Kithdara/Simple-Voice-Recorder/Prototype on breadboard.jpeg

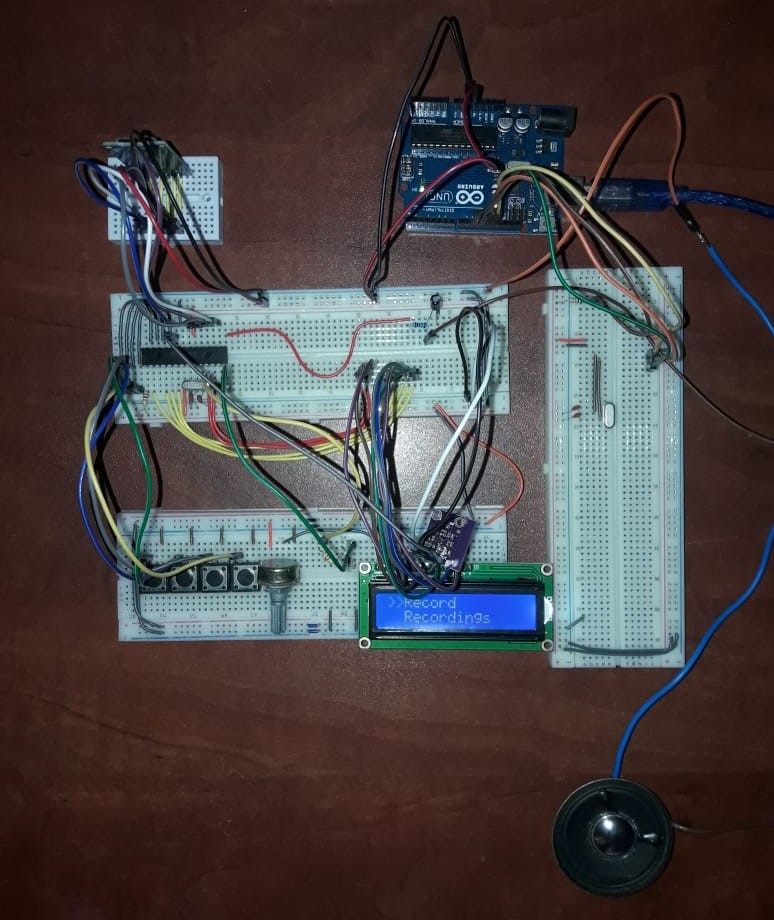
Prototype on breadboard.jpeg
