Kithdara/Simple-Voice-Recorder/simulations of spectrum changes/Downsampling/Photos/DownSampling Spectrum.png

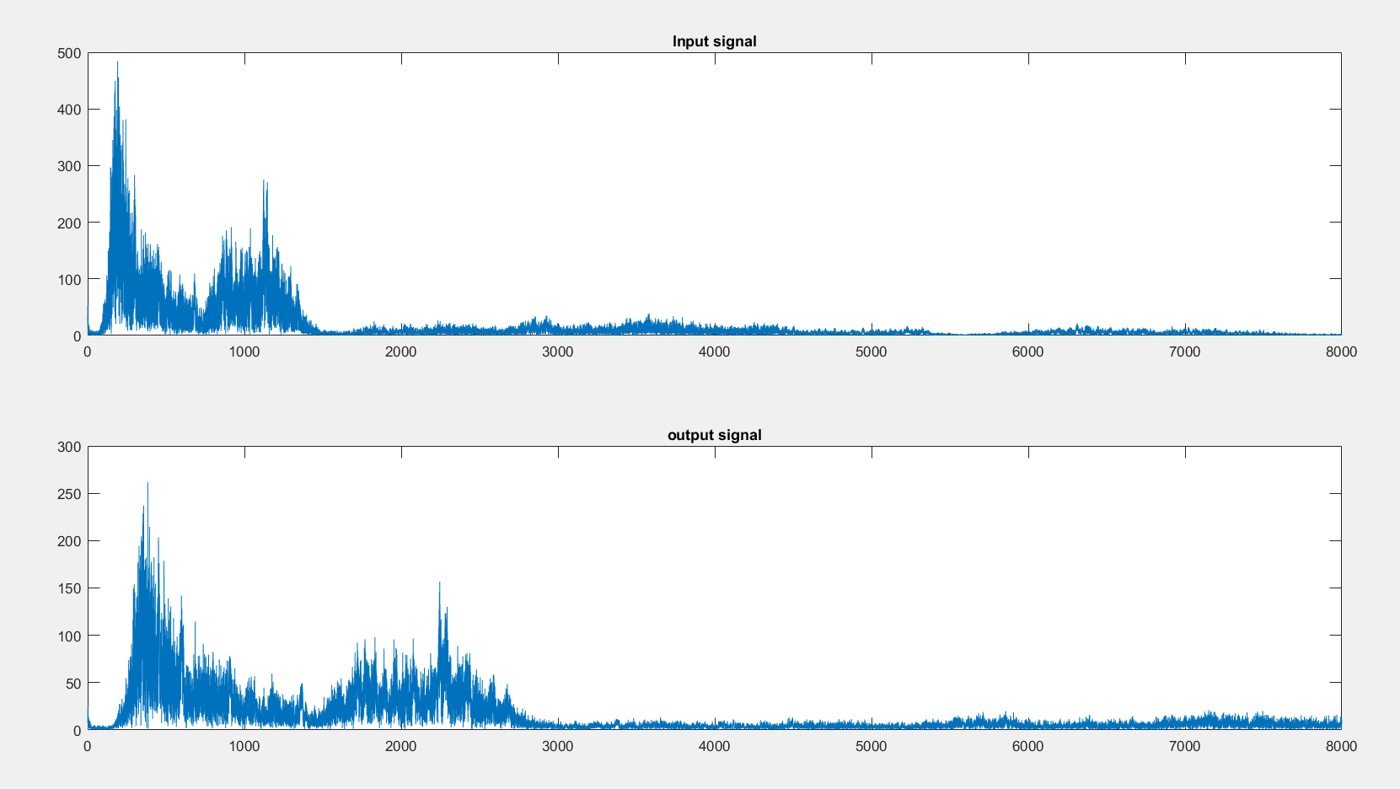
simulations of spectrum changes/Downsampling/Photos/DownSampling Spectrum.png
