Kithdara/Simple-Voice-Recorder/Final Enclousre Design/battery-9v-pile-9v-1.snapshot.1/Connecteur femelle Batterie 9V.SLDPRT

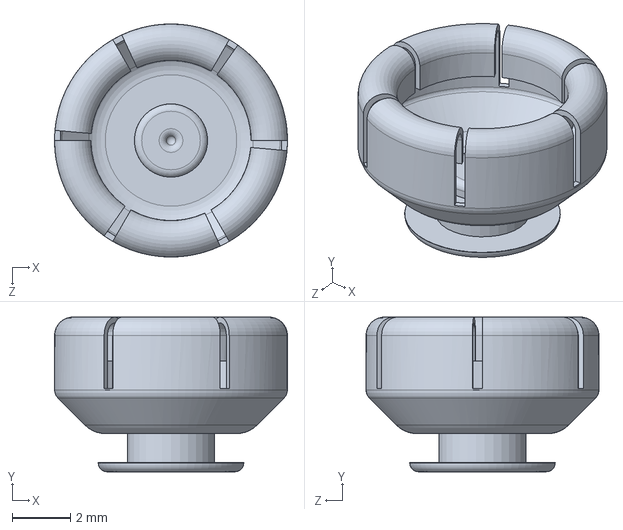
[picture p45: CAD file, 2021-09-02]
Final Enclousre Design/battery-9v-pile-9v-1.snapshot.1/Connecteur femelle Batterie 9V.SLDPRT
8.00 x 5.31 x 8.00 mm
