Kithdara/Simple-Voice-Recorder/Final Enclousre Design/Name plate.SLDPRT

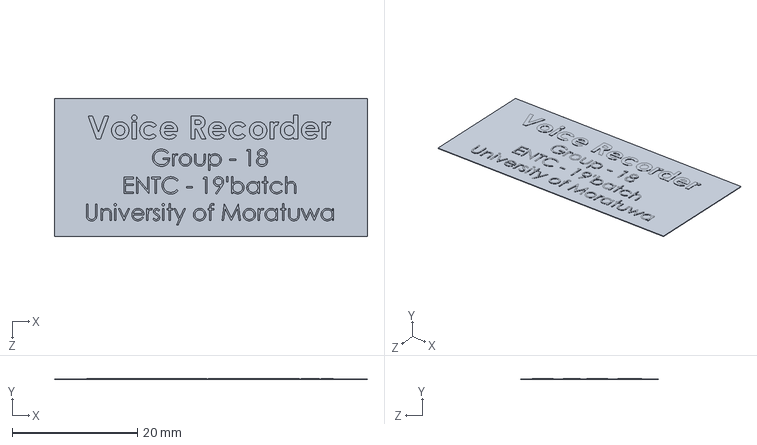
[picture p46: CAD file, 2021-09-02]
Final Enclousre Design/Name plate.SLDPRT
50.0 x 0.15 x 22.0 mm
