Kithdara/Simple-Voice-Recorder/Final Enclousre Design/battery-9v-pile-9v-1.snapshot.1/Corps Batterie.SLDPRT

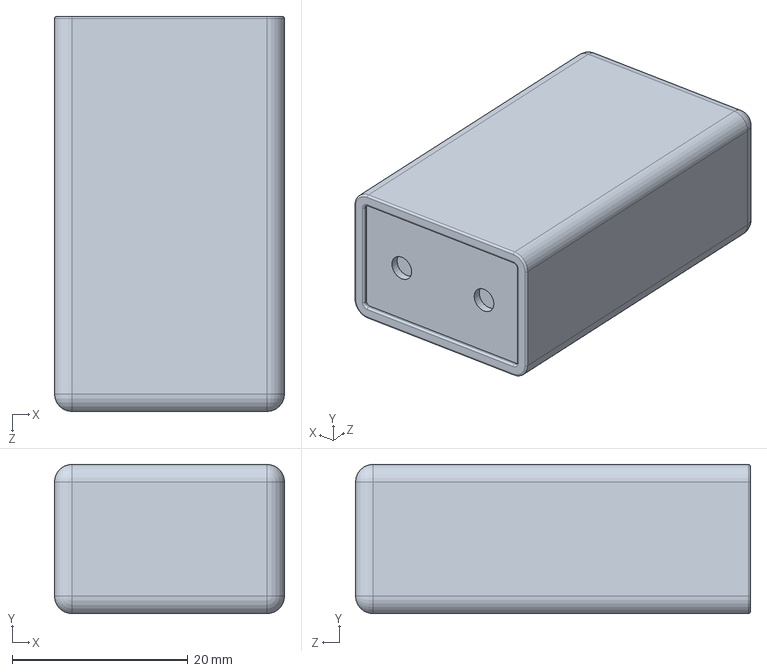
[picture p47: CAD file, 2021-09-02]
Final Enclousre Design/battery-9v-pile-9v-1.snapshot.1/Corps Batterie.SLDPRT
26.2 x 17.0 x 45.0 mm
