Kithdara/Simple-Voice-Recorder/Final Enclousre Design/button.SLDPRT

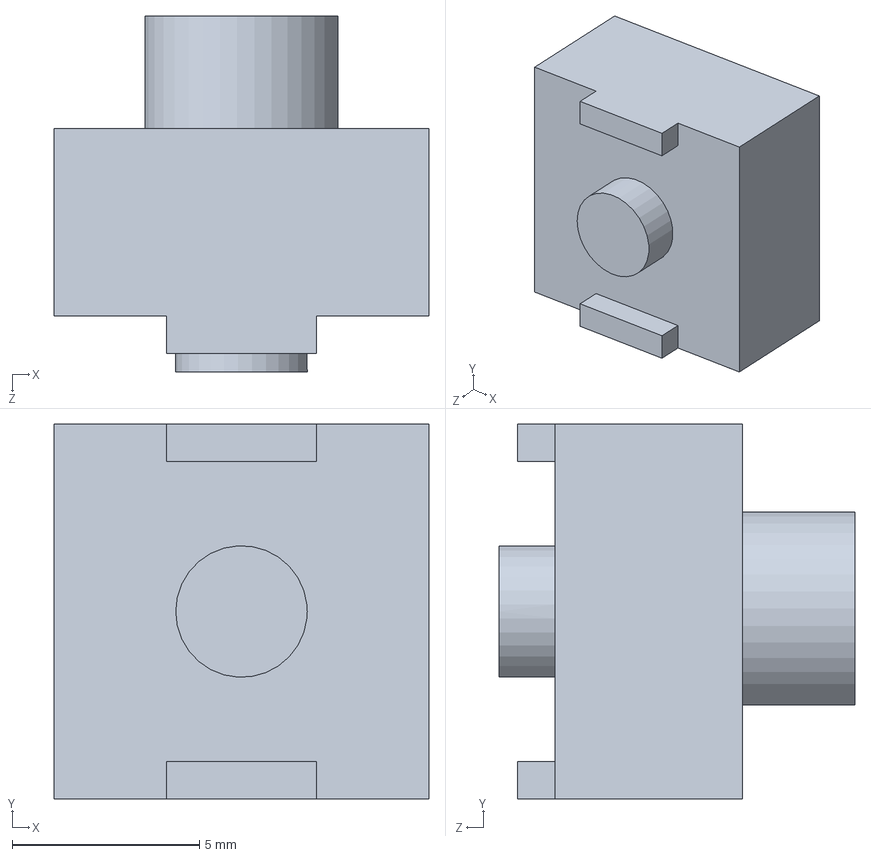
[picture p48: CAD file, 2021-09-02]
Final Enclousre Design/button.SLDPRT
10.0 x 10.0 x 9.50 mm
