Kithdara/Simple-Voice-Recorder/Final Enclousre Design/battery-9v-pile-9v-1.snapshot.1/Connecteur male Batterie 9V.SLDPRT

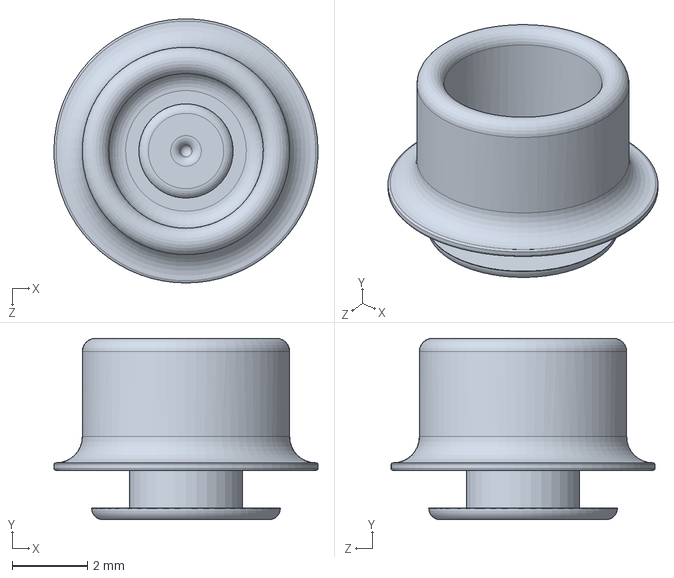
[picture p49: CAD file, 2021-09-02]
Final Enclousre Design/battery-9v-pile-9v-1.snapshot.1/Connecteur male Batterie 9V.SLDPRT
7.00 x 4.81 x 7.00 mm
