Kithdara/Simple-Voice-Recorder/Final Enclousre Design/recorder top.SLDPRT

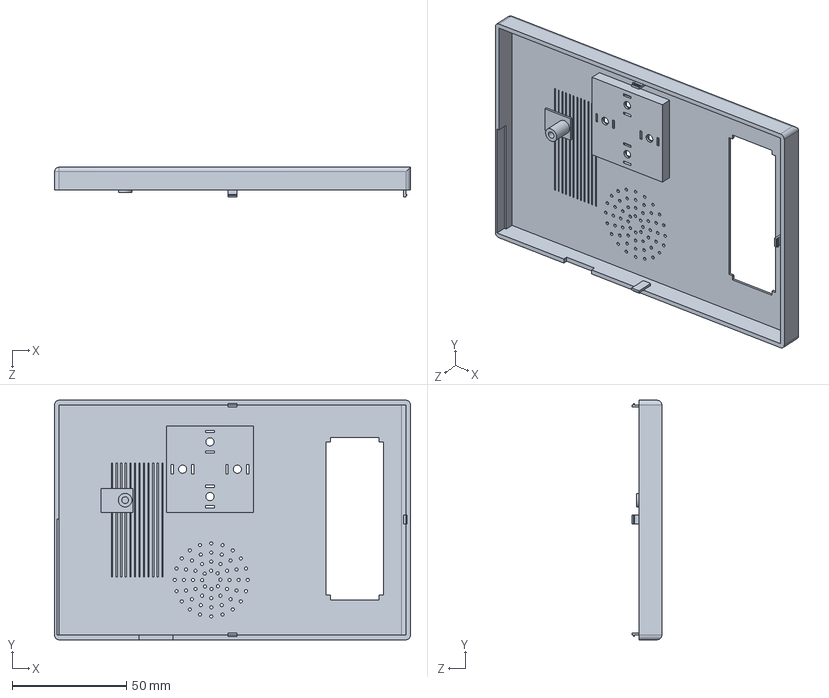
[picture p50: CAD file, 2021-09-02]
Final Enclousre Design/recorder top.SLDPRT
156.0 x 105.0 x 13.0 mm
