Kithdara/Simple-Voice-Recorder/Final Enclousre Design/battery cover.SLDPRT

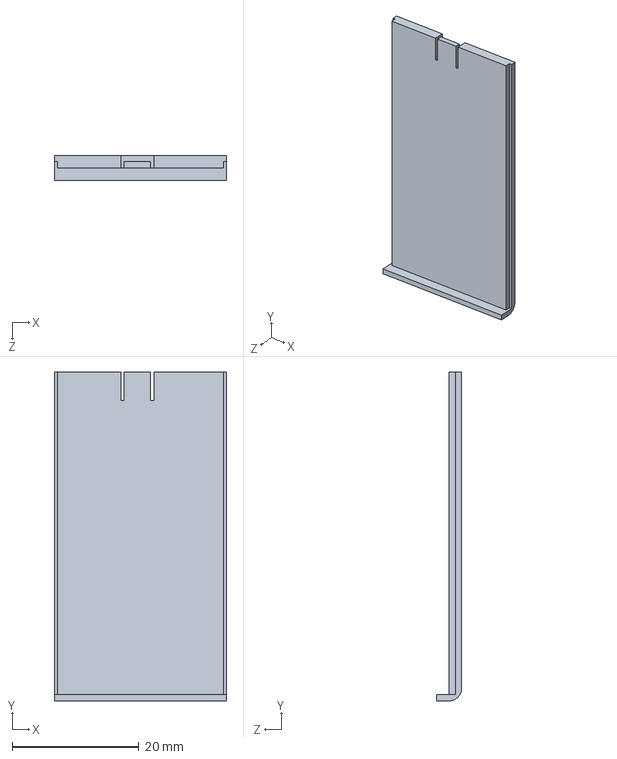
[picture p51: CAD file, 2021-09-02]
Final Enclousre Design/battery cover.SLDPRT
27.2 x 52.0 x 4.00 mm
