Kithdara/Simple-Voice-Recorder/Final Enclousre Design/recorder bottom.SLDPRT

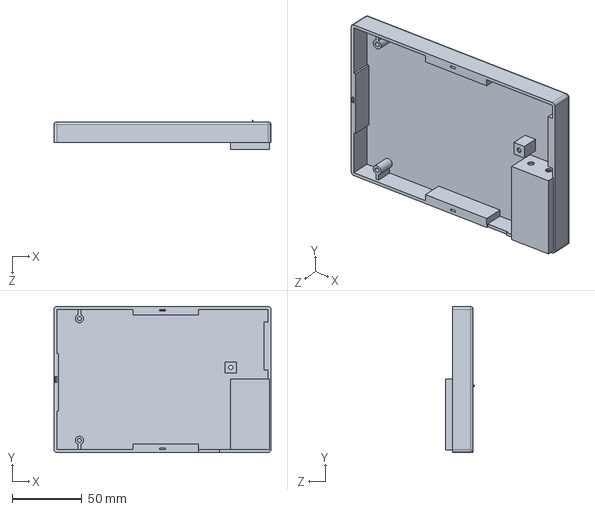
[picture p52: CAD file, 2021-09-02]
Final Enclousre Design/recorder bottom.SLDPRT
156.0 x 105.0 x 21.0 mm
