Kithdara/Simple-Voice-Recorder/simulations of spectrum changes/Frequncey_shift/Photos/Input Signal & Shifted Output Signal (Arduino).png

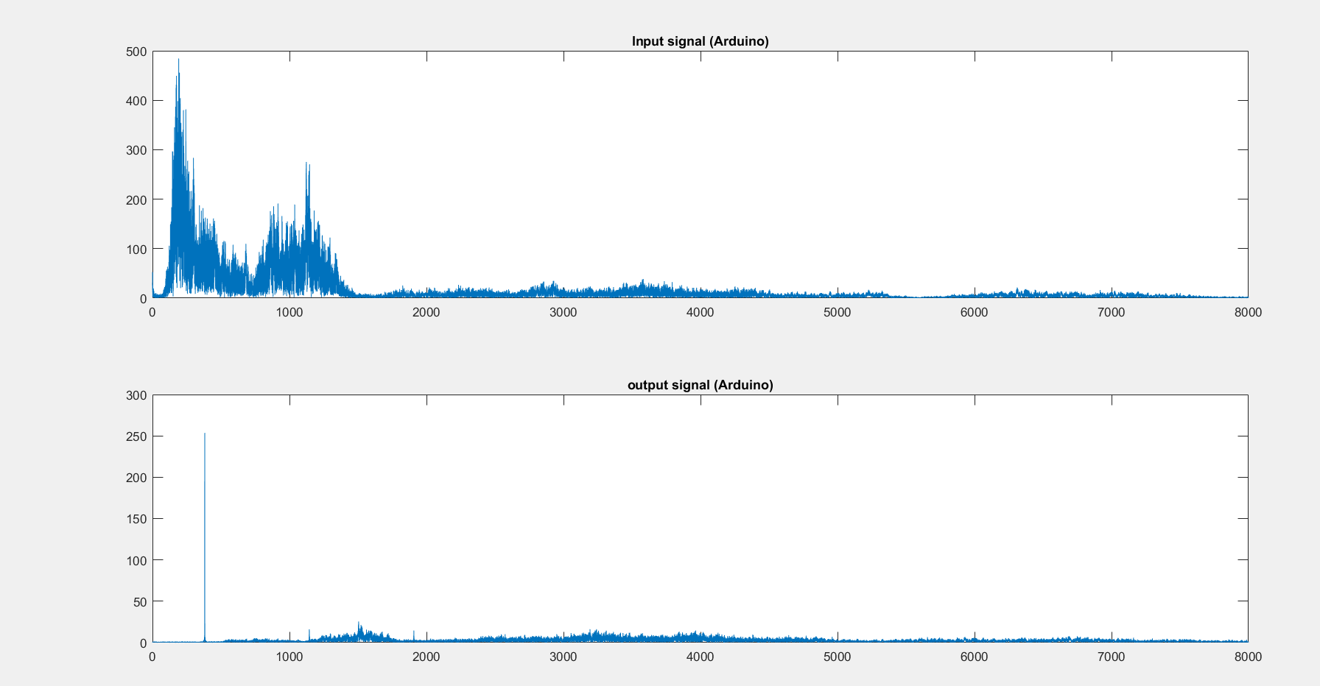
simulations of spectrum changes/Frequncey_shift/Photos/Input Signal & Shifted Output Signal (Arduino).png
