Kithdara/Simple-Voice-Recorder/simulations of spectrum changes/Frequncey_shift/Photos/Shifted output Signal Arduino.png

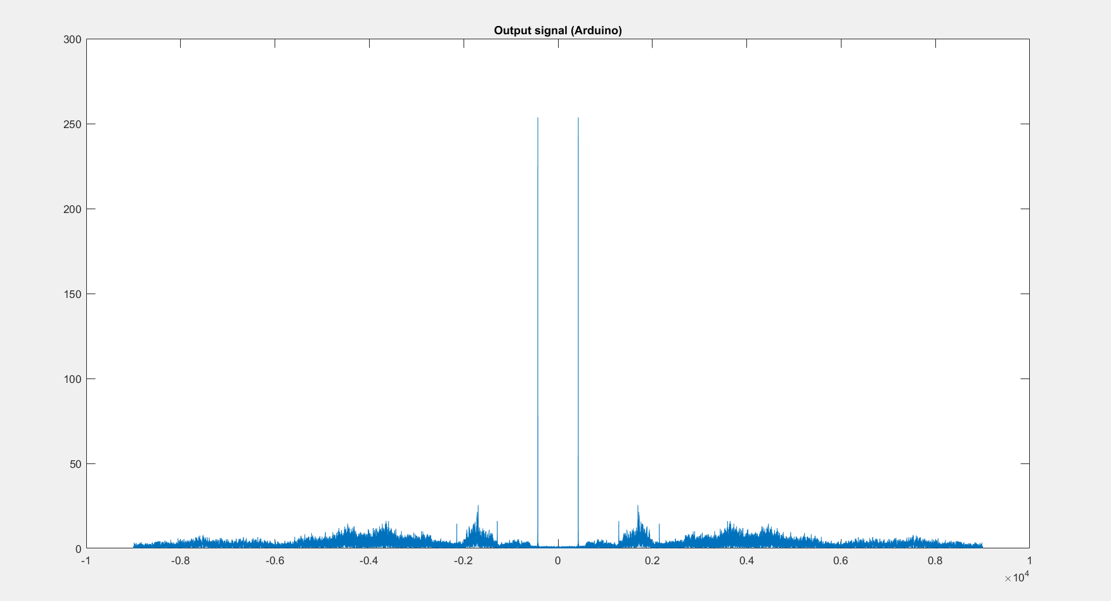
simulations of spectrum changes/Frequncey_shift/Photos/Shifted output Signal Arduino.png
